Salted-Peanuts/KOTH-Timer/Images/PCB1.jpg

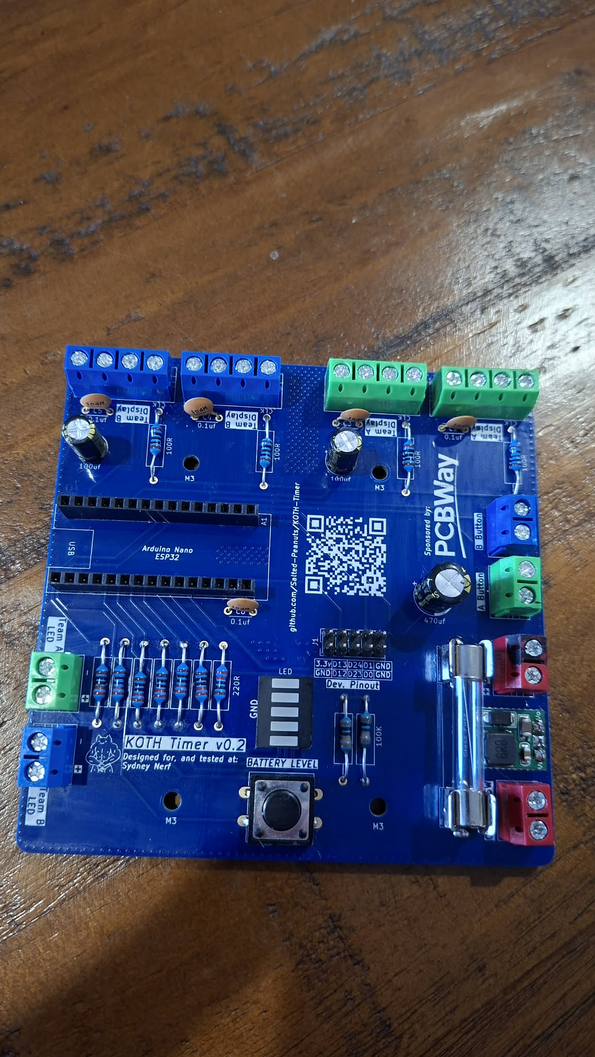
Images/PCB1.jpg
