Salted-Peanuts/KOTH-Timer/Images/Prototype_ref_2.jpg

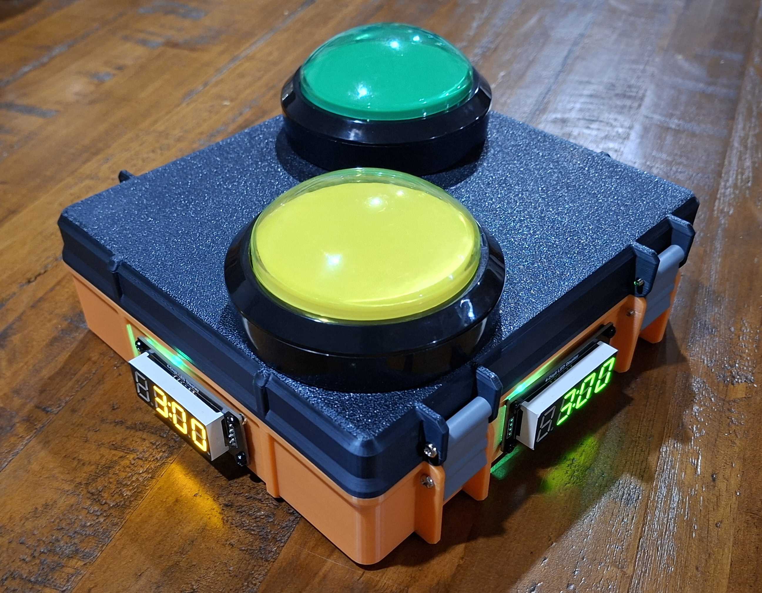
Images/Prototype_ref_2.jpg
