Salted-Peanuts/KOTH-Timer/Images/v0.2_All_Layers.JPG

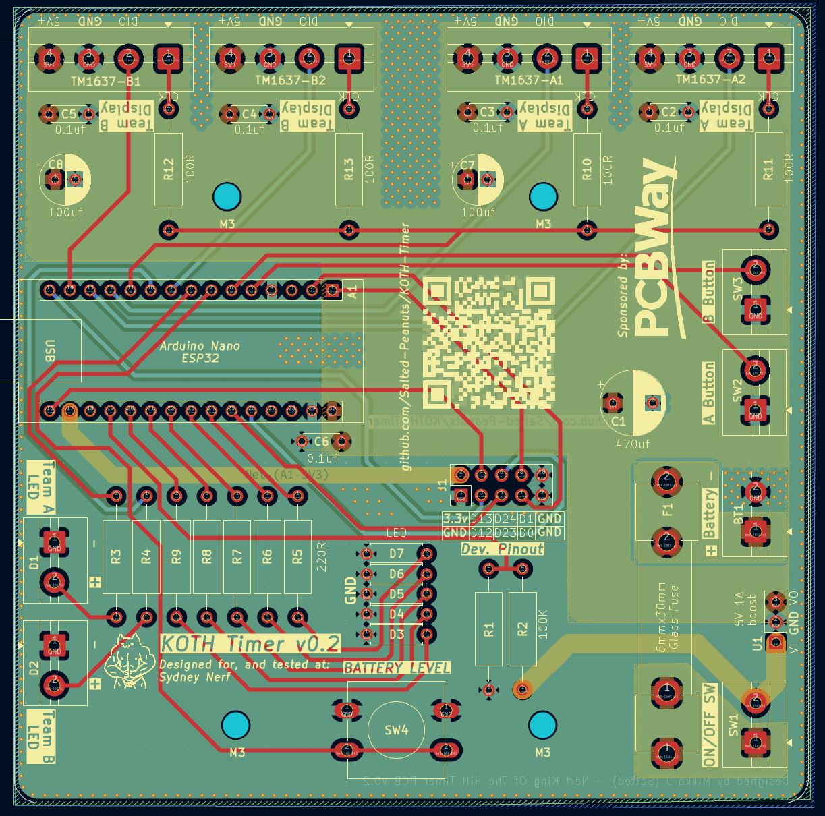
Images/v0.2_All_Layers.JPG
