Salted-Peanuts/KOTH-Timer/Images/v0.2_BACK.JPG

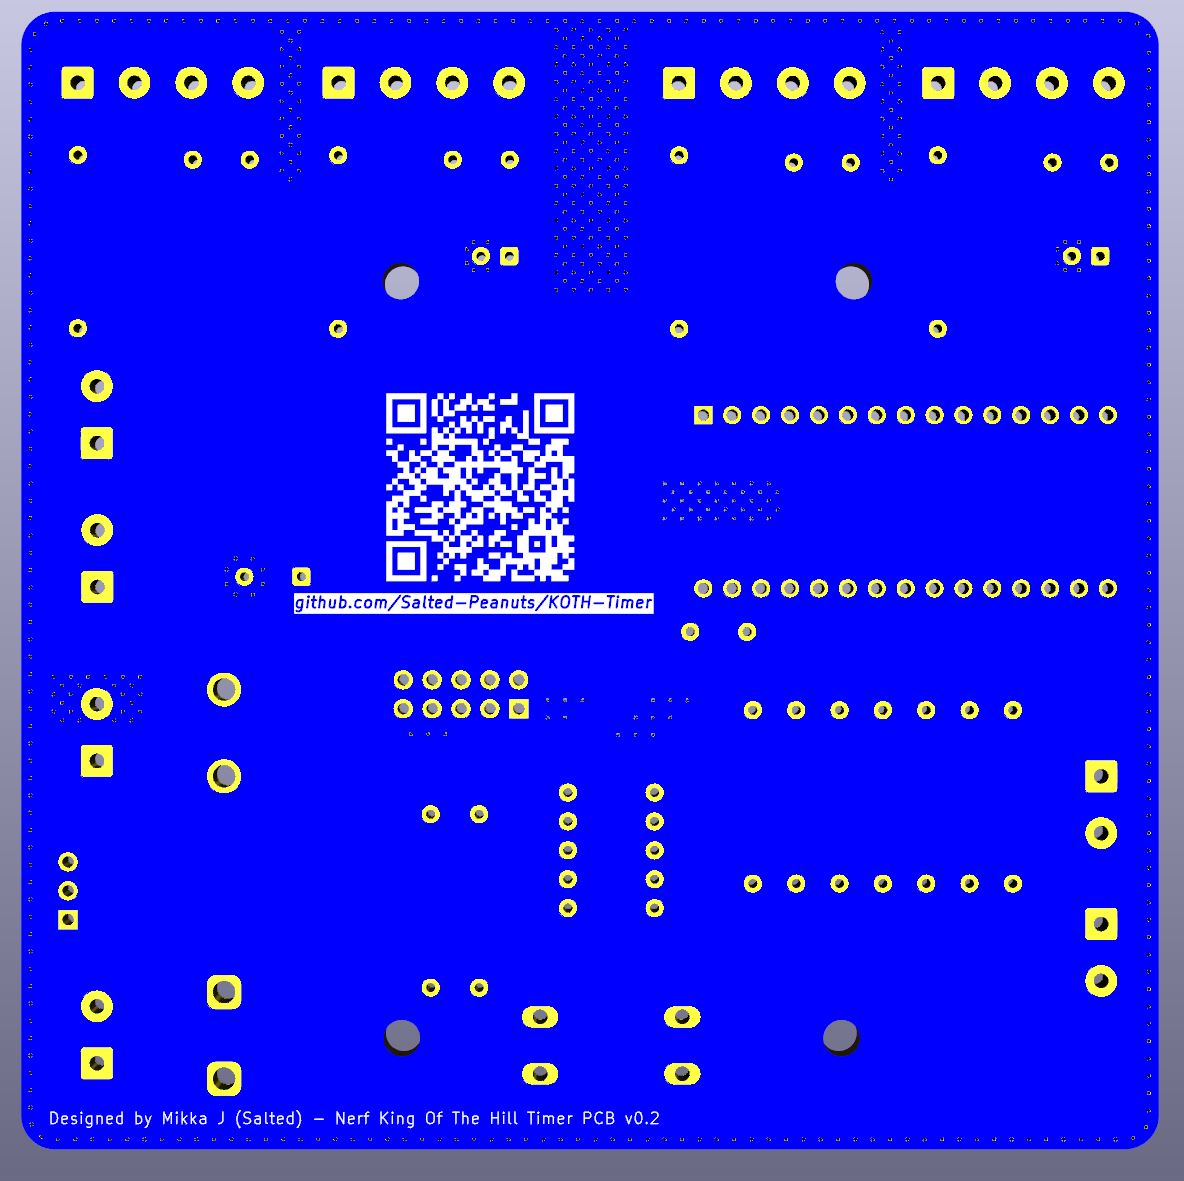
Images/v0.2_BACK.JPG
