Salted-Peanuts/KOTH-Timer/Images/v0.2_Render.JPG

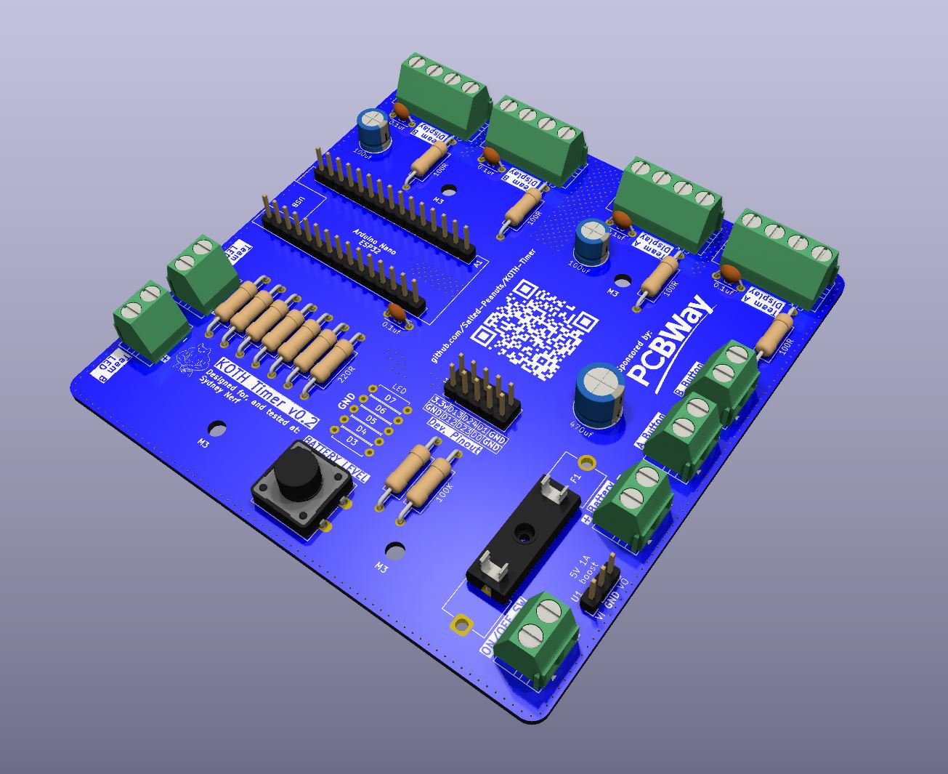
Images/v0.2_Render.JPG
